nitram509/temperature-based-fan-control-for-time-capsule/20151025_181111.jpg

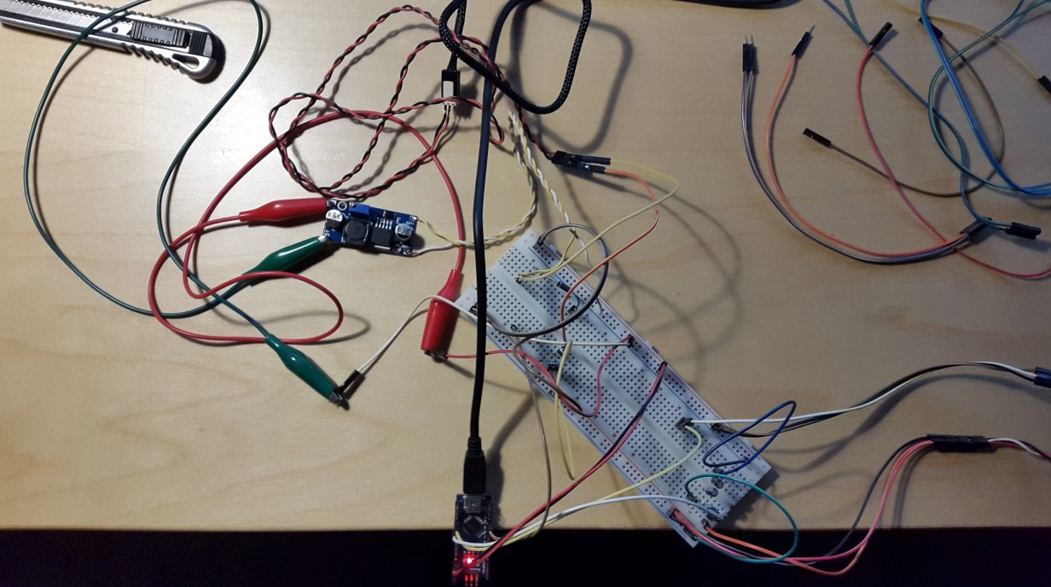
20151025_181111.jpg
